kuzmin-no/ELKO_GLED316_dimmer/img/Connection_diagram.png

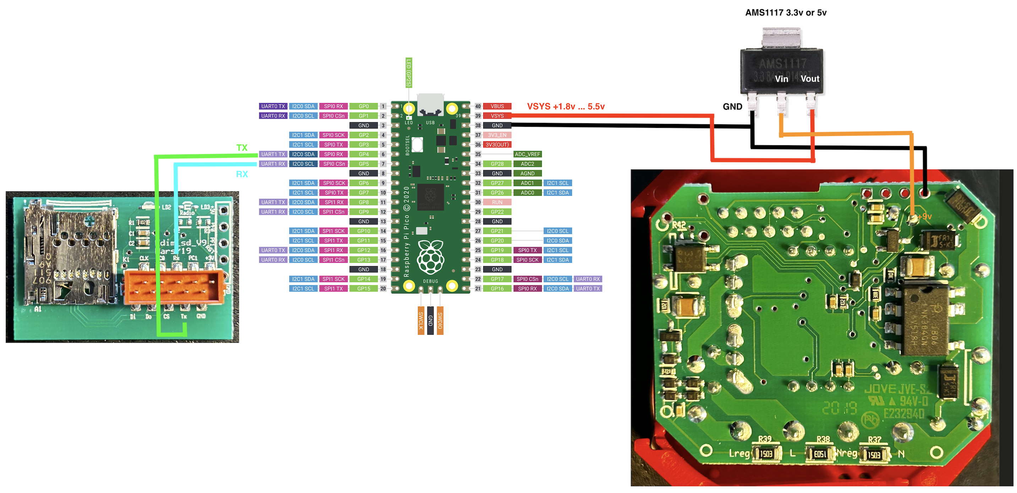
img/Connection_diagram.png
