kuzmin-no/ELKO_GLED316_dimmer/img/GLED316_back.jpg

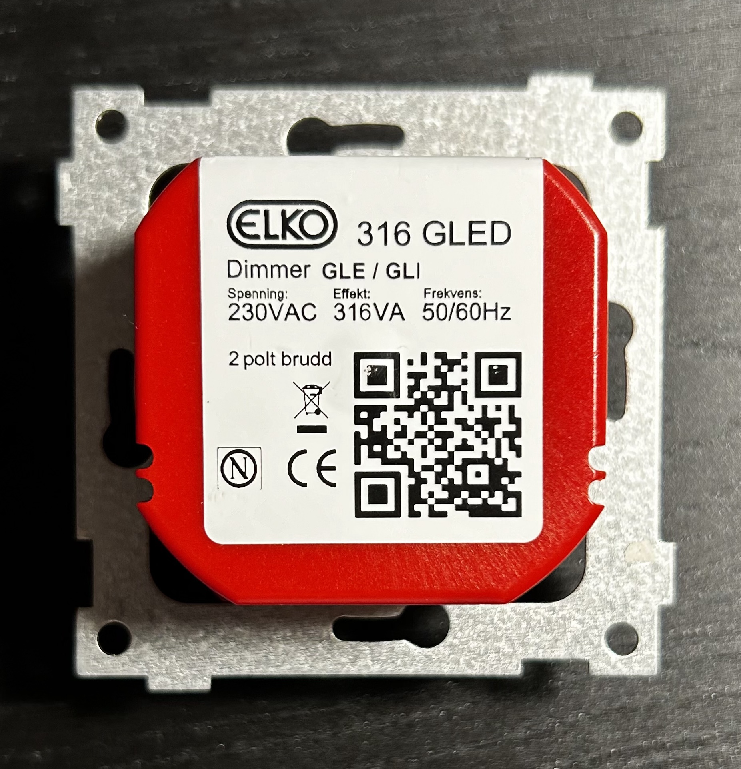
img/GLED316_back.jpg
