kuzmin-no/ELKO_GLED316_dimmer/img/GLED316_front.jpg

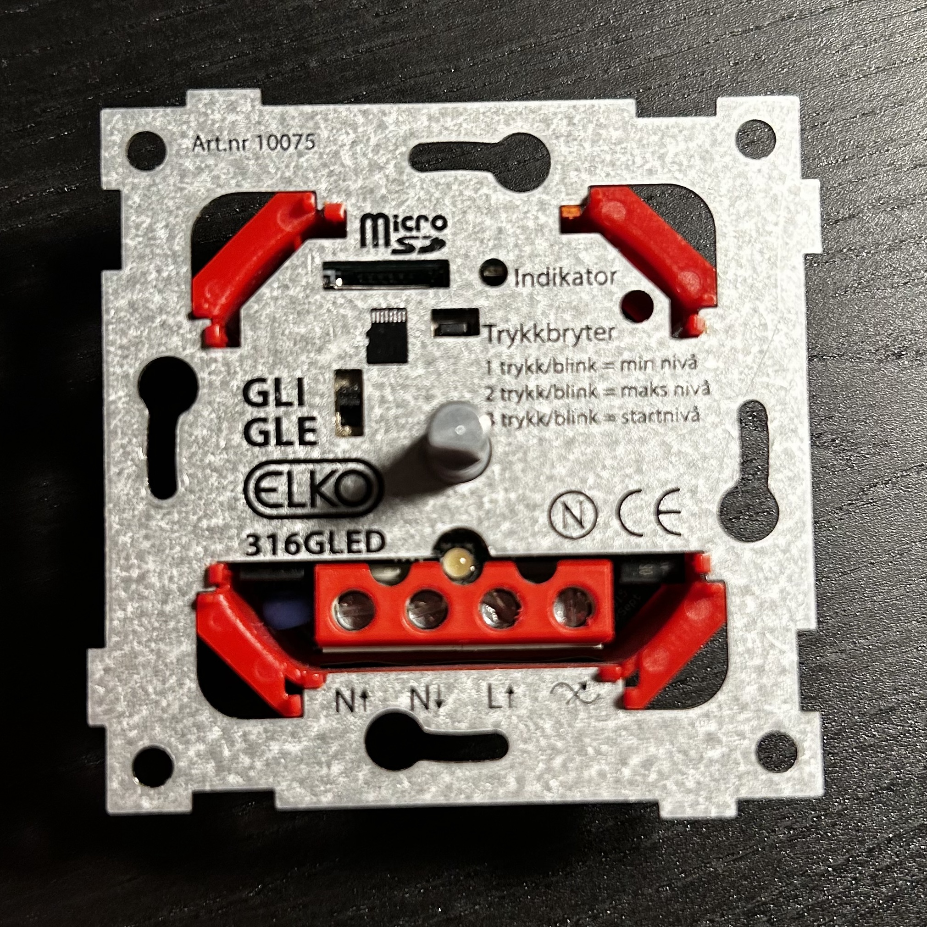
img/GLED316_front.jpg
