kuzmin-no/ELKO_GLED316_dimmer/img/GLED316_smartdim2.png

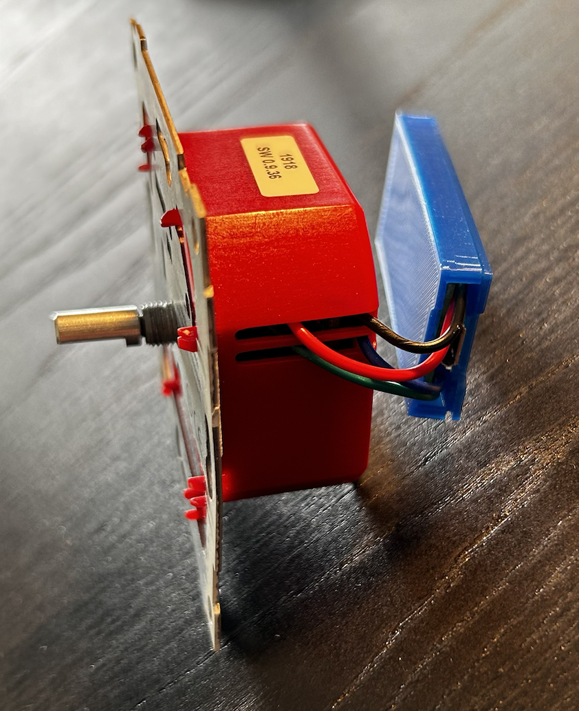
img/GLED316_smartdim2.png
